n01103934/Thermometer/documentation/Week3RubricforProjectSchedule.jpg

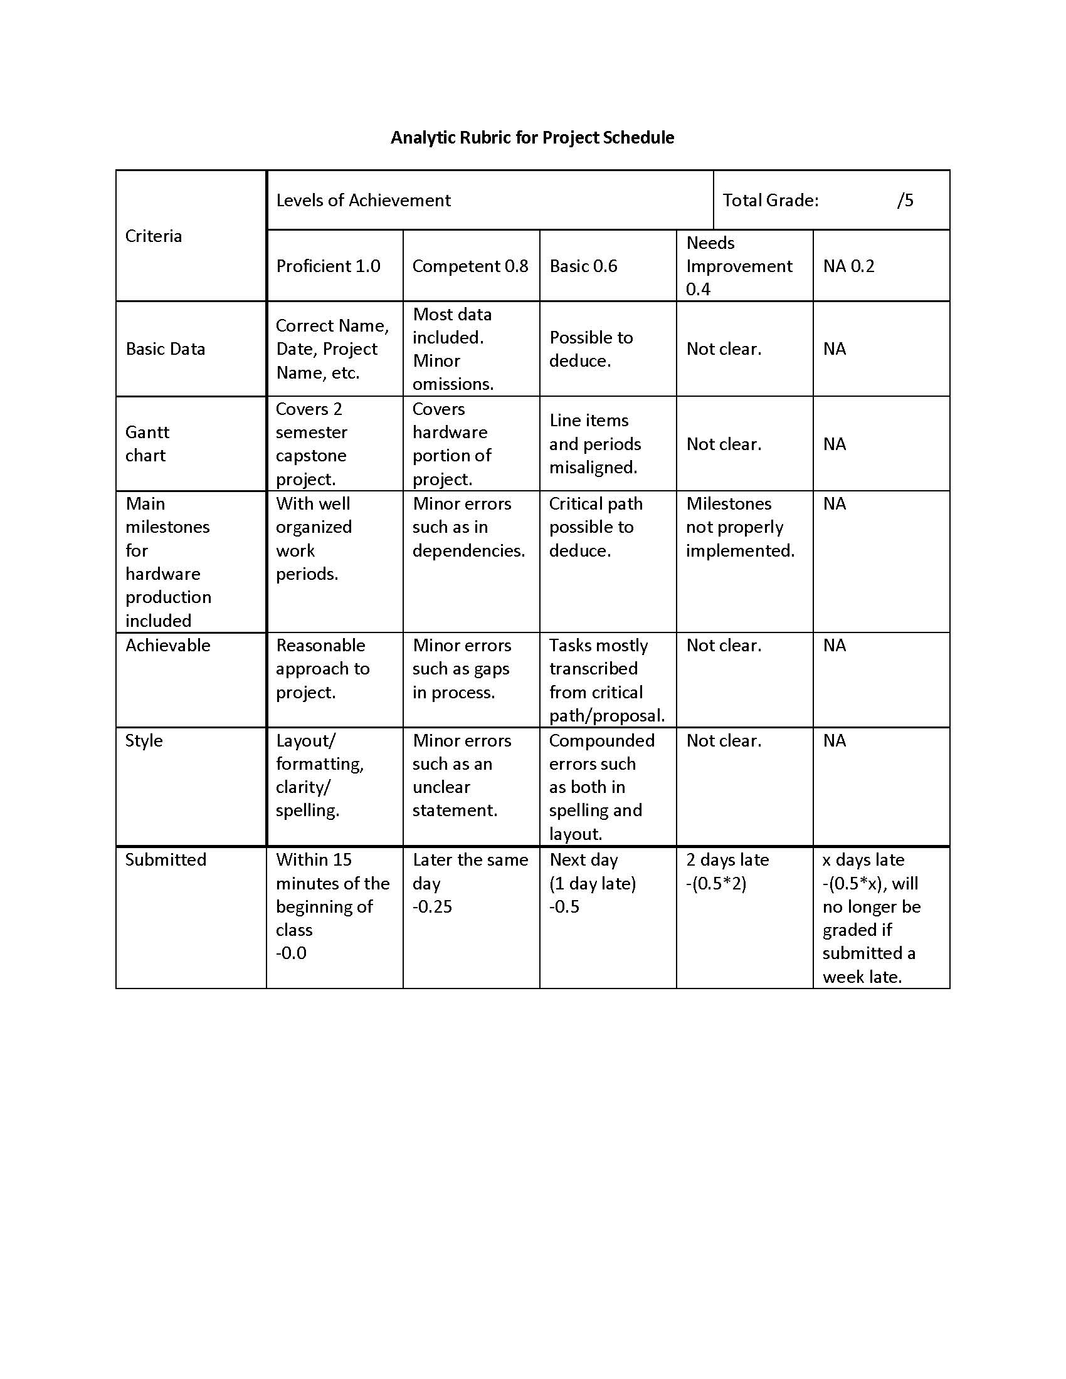
documentation/Week3RubricforProjectSchedule.jpg
