n01103934/Thermometer/images/parts.png

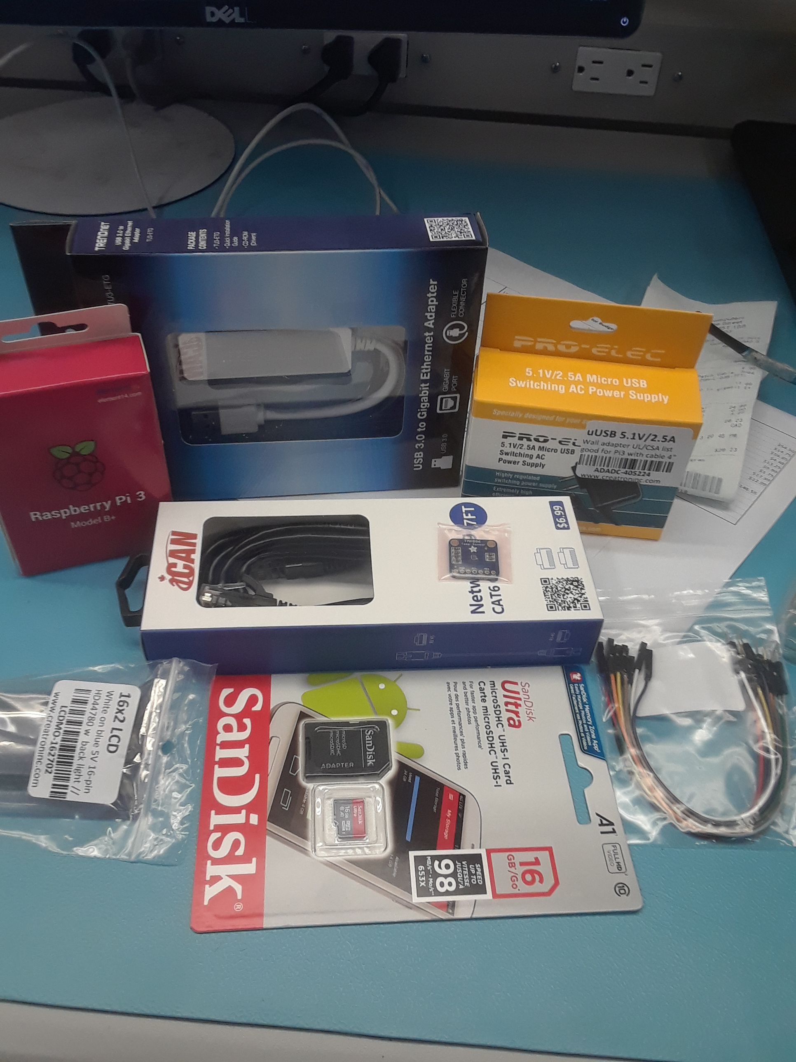
images/parts.png
